aerospace-venoms/BCCC_Temperature_SAO/src/temp.h

#pragma once
#include <stdbool.h>

// Initialise whichever sensor is available.
// Probes for DS18B20 first; if absent, falls back to the RP2350 internal
// ADC temperature sensor.  Call once at startup.
void temp_init(void);

// True if a DS18B20 was detected at startup.
bool temp_has_ds18b20(void);

// Read the current temperature in degrees Celsius.
float temp_read_c(void);

// Read the current temperature in degrees Fahrenheit.
// Uses DS18B20 if available, otherwise the internal ADC sensor.
float temp_read_f(void);

// Read the RP2350 internal ADC temperature sensor directly (die temperature,
// not ambient).  Always available regardless of DS18B20 presence.
float temp_read_internal_f(void);
